ctlvie/Spectrum-Characteristic-Tester/src/Spectrum-Characteristic-Tester/Button.c

/*=======================================================
Author			    :				ctlvie
Email Address		:				ctlvie@gmail.com
Filename	        :				Button.c
Date				:		        2018-11-22
Description			:				LaunchPad片上按键控制

Modification History:
Date		By			Version		Description
----------------------------------------------------------
181122		ctlvie		1.0			功能实现
181216      ctlvie      2.0         Final Version
========================================================*/

#include <msp430f5529.h>
#include "Button.h"
volatile int key_pre_cnt = 0;
volatile int interrupt_key = 0;
extern volatile int Button_S1; //should be defined in the "main.c" as a global varible
extern volatile int Button_S2; //should be defined in the "main.c" as a global varible
extern volatile int Button_S3; //should be defined in the "main.c" as a global varible
extern volatile int Button_S4; //should be defined in the "main.c" as a global varible

extern int t ;

void initButtonsTimer(void)
{
    TA0CCTL0 = CCIE;
    TA0CCR0 = 10000;
    TA0CTL = TASSEL_2 + MC_1 + TACLR;
}

void initButtons(void)
{
    _DINT();
    IO_BUTTON_S2_REN |= IO_BUTTON_BIT_S2;
    IO_BUTTON_S2_OUT |= IO_BUTTON_BIT_S2;
    IO_BUTTON_S2_DIR &= IO_BUTTON_BIT_S2;
    IO_BUTTON_S2_IES |= IO_BUTTON_BIT_S2;
    IO_BUTTON_S2_IFG &= ~IO_BUTTON_BIT_S2;
    IO_BUTTON_S2_IE |=  IO_BUTTON_BIT_S2;

    IO_BUTTON_S1_REN |= IO_BUTTON_BIT_S1;
    IO_BUTTON_S1_OUT |= IO_BUTTON_BIT_S1;
    IO_BUTTON_S1_DIR &= IO_BUTTON_BIT_S1;
    IO_BUTTON_S1_IES |= IO_BUTTON_BIT_S1;
    IO_BUTTON_S1_IFG &= ~IO_BUTTON_BIT_S1;
    IO_BUTTON_S1_IE |=  IO_BUTTON_BIT_S1;

    IO_BUTTON_S3_REN |= IO_BUTTON_BIT_S3;
    IO_BUTTON_S3_OUT |= IO_BUTTON_BIT_S3;
    IO_BUTTON_S3_DIR &= IO_BUTTON_BIT_S3;
    IO_BUTTON_S3_IES |= IO_BUTTON_BIT_S3;
    IO_BUTTON_S3_IFG &= ~IO_BUTTON_BIT_S3;
    IO_BUTTON_S3_IE |=  IO_BUTTON_BIT_S3;

    IO_BUTTON_S4_REN |= IO_BUTTON_BIT_S4;
    IO_BUTTON_S4_OUT |= IO_BUTTON_BIT_S4;
    IO_BUTTON_S4_DIR &= IO_BUTTON_BIT_S4;
    IO_BUTTON_S4_IES |= IO_BUTTON_BIT_S4;
    IO_BUTTON_S4_IFG &= ~IO_BUTTON_BIT_S4;
    IO_BUTTON_S4_IE |=  IO_BUTTON_BIT_S4;
    
    Button_S1 = 0;
    Button_S2 = 0;
    Button_S3 = 0;
    Button_S4 = 0;

    initButtonsTimer();
    _EINT();
}


#pragma vector=PORT1_VECTOR
__interrupt void Port_1(void)
{
    t ++;
    if(IO_BUTTON_S2_IFG&IO_BUTTON_BIT_S2)
    {

        if (key_pre_cnt < BUTTON_THRESHOLD) 
            Button_S2 = Button_S2;
        else
        {
            Button_S2 = 1;
            key_pre_cnt=0;
        }
        IO_BUTTON_S2_IFG &=~ IO_BUTTON_BIT_S2;
        IO_BUTTON_S2_IFG = 0;
        IO_BUTTON_S2_IES |= IO_BUTTON_BIT_S2;
        IO_BUTTON_S2_IE |= IO_BUTTON_BIT_S2;
    }
    else if(IO_BUTTON_S1_IFG&IO_BUTTON_BIT_S1)
    {
        if (key_pre_cnt < BUTTON_THRESHOLD) 
            Button_S1=Button_S1;
        else
        {
            Button_S1 = 1;
            key_pre_cnt=0;
        } 
        IO_BUTTON_S1_IFG &=~ IO_BUTTON_BIT_S1;
        IO_BUTTON_S1_IFG = 0;
        IO_BUTTON_S1_IES |= IO_BUTTON_BIT_S1;
        IO_BUTTON_S1_IE |= IO_BUTTON_BIT_S1;    
    }
    else if(IO_BUTTON_S3_IFG&IO_BUTTON_BIT_S3)
    {
        if (key_pre_cnt < BUTTON_THRESHOLD) 
            Button_S3=Button_S3;
        else
        {
            Button_S3 = 1;
            key_pre_cnt=0;
        } 
        IO_BUTTON_S3_IFG &=~ IO_BUTTON_BIT_S3;
        IO_BUTTON_S3_IFG = 0;
        IO_BUTTON_S3_IES |= IO_BUTTON_BIT_S3;
        IO_BUTTON_S3_IE |= IO_BUTTON_BIT_S3;    
    }
    else if(IO_BUTTON_S4_IFG&IO_BUTTON_BIT_S4)
    {
        if (key_pre_cnt < BUTTON_THRESHOLD) 
            Button_S4=Button_S4;
        else
        {
            Button_S4 = 1;
            key_pre_cnt=0;
        } 
        IO_BUTTON_S4_IFG &=~ IO_BUTTON_BIT_S4;
        IO_BUTTON_S4_IFG = 0;
        IO_BUTTON_S4_IES |= IO_BUTTON_BIT_S4;
        IO_BUTTON_S4_IE |= IO_BUTTON_BIT_S4;    
    }




}



#pragma vector=TIMER0_A0_VECTOR
__interrupt void TIMER0_A0_ISR (void)
{
    key_pre_cnt ++;
}
